flas-tech/cj2-voice-emergency-checklist/ip/trademark_findings.md

# Trademark Availability Screening
## Voice-Driven Emergency Checklist Reader for Aircraft
**Search platform:** USPTO Trademark Search (tmsearch.uspto.gov) · **Date:** June 2026 · **Search type:** wordmark
**Most relevant classes:** IC 009 (electronic/avionics devices, downloadable software), IC 042 (SaaS/software services)

> Not legal advice. A registered trademark attorney should run a full clearance search (state, common-law, and design-mark) before adoption.

## Results by candidate

| # | Name | Live results | Class 9 / 42 conflict | Risk | Verdict |
|---|---|---|---|---|---|
| 1 | AeroVox | 1 | LIVE Class 9 — capacitors (CD Aero LLC, Ser. 77409823) | Moderate | Consult attorney |
| 2 | VoxPilot | 1 | **LIVE Class 9 — speech-recognition software (Reg. 4551726)** | **High** | **Avoid** |
| 3 | AviVox | 0 | None | Clear | Strong candidate |
| 4 | VoxCheck | 0 | None | Clear | Strong candidate |
| 5 | AeroCheck | 1 | LIVE Class 7 — hydraulic check valves (Eaton, Ser. 78433687) | Moderate | Consult attorney |
| 6 | Litany | 2 | None in 9/42 (jewelry, photo website) | Clear but weak | Viable, low distinctiveness |
| 7 | Wingman | 125 live (20+ in Class 9) | Crowded; aviation marks (Beeper Avionics) DEAD | Moderate-High | Caution |
| 8 | CheckCall | 0 | None | Clear | Strong candidate |

## Detail on the decisive ones

- **VoxPilot — AVOID.** Identical wordmark, LIVE/REGISTERED in Class 9 for "software for reporting real-time analytics generated from interactive speech recognition applications" (Reg. No. 4551726, Ser. 86113375). Directly analogous to our voice-recognition product → near-certain refusal and opposition risk.
- **AeroVox — moderate.** LIVE Class 9 registration for capacitors (CD Aero LLC, Ser. 77409823). Different goods, but Class 9 is broad and an examiner could cite it.
- **Wingman — crowded.** 20+ live Class 9 marks (sunglasses, flotation vests, speakers, automotive driver-assist, etc.). Notably, the only *aviation-specific* Wingman marks — Beeper Avionics' "portable electronic device for detecting/locating aircraft" (Ser. 88947677) and "software for generating audible aircraft warnings/checklists" (Ser. 88984394) — are both DEAD/ABANDONED. The aviation niche is technically open but the name is weak and heavily contested.
- **AviVox / VoxCheck / CheckCall — clear.** Zero results in any class. Safest to register; strong inherent distinctiveness (coined/suggestive).
- **Litany — clear but weak.** No 9/42 conflicts, but it's a common English word (low distinctiveness, hard to enforce).

## Recommendation (for the report)
Lead candidate: **AviVox** (coined, aviation + voice, clean across all classes). Backups: **VoxCheck**, **CheckCall**. All three are inherently distinctive and currently unregistered. Confirm common-law/domain use before adoption.
