flas-tech/cj2-voice-emergency-checklist/ip/figures/patent_figures.pdf

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

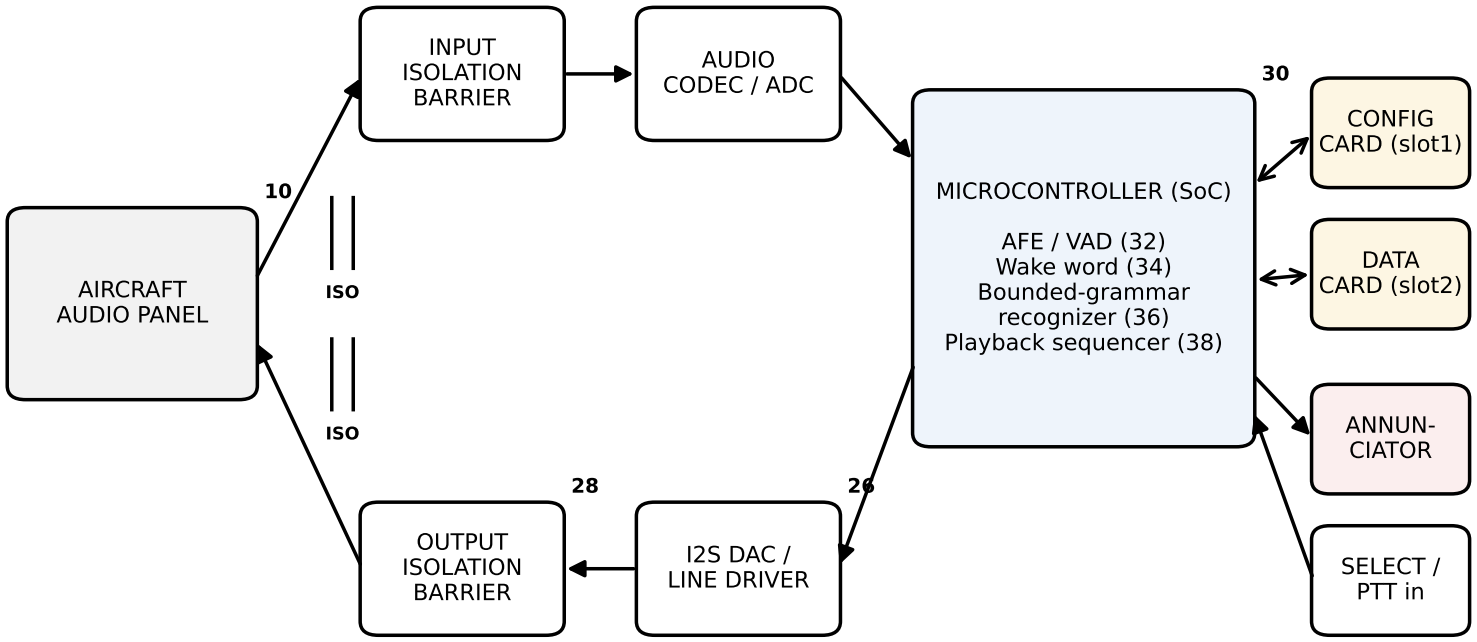
[picture p16: figure]

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

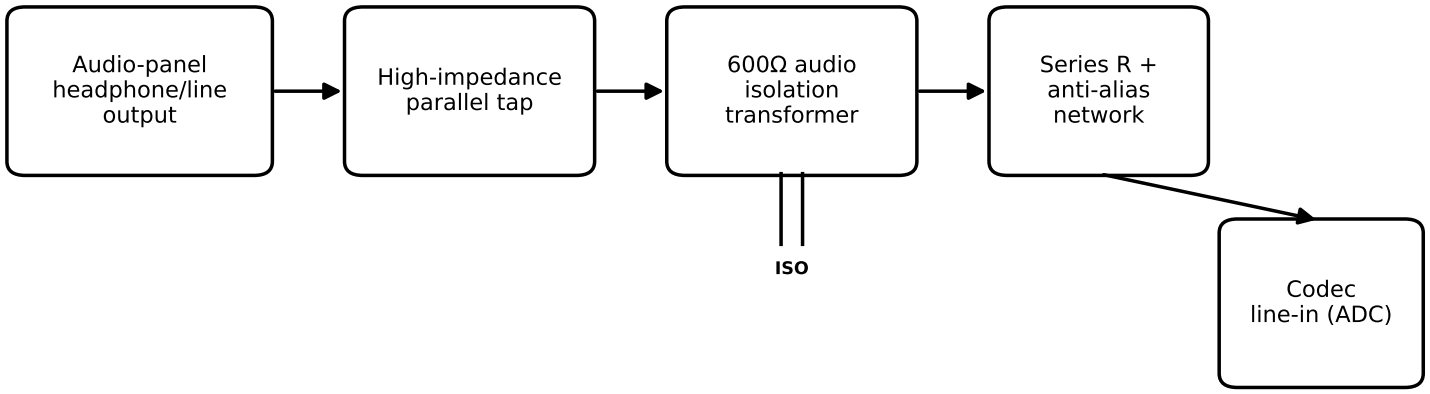
[picture p17: figure]

# FIG. 3

## Digital Audio-Input Embodiment (Buffered, Receive-Only)

10

21b
24

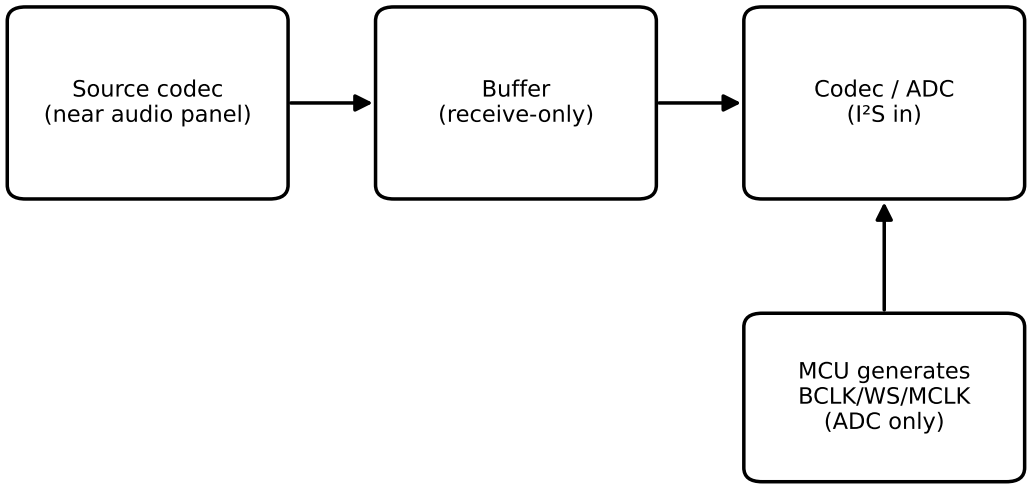
[picture p18: figure]
Source codec (near audio panel); Buffer (receive-only); Codec / ADC (I²S in); MCU generates BCLK/WS/MCLK (ADC only)

25

data: panel device only

All clocks generated locally for the ADC; no data line is driven back toward any aircraft bus.

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

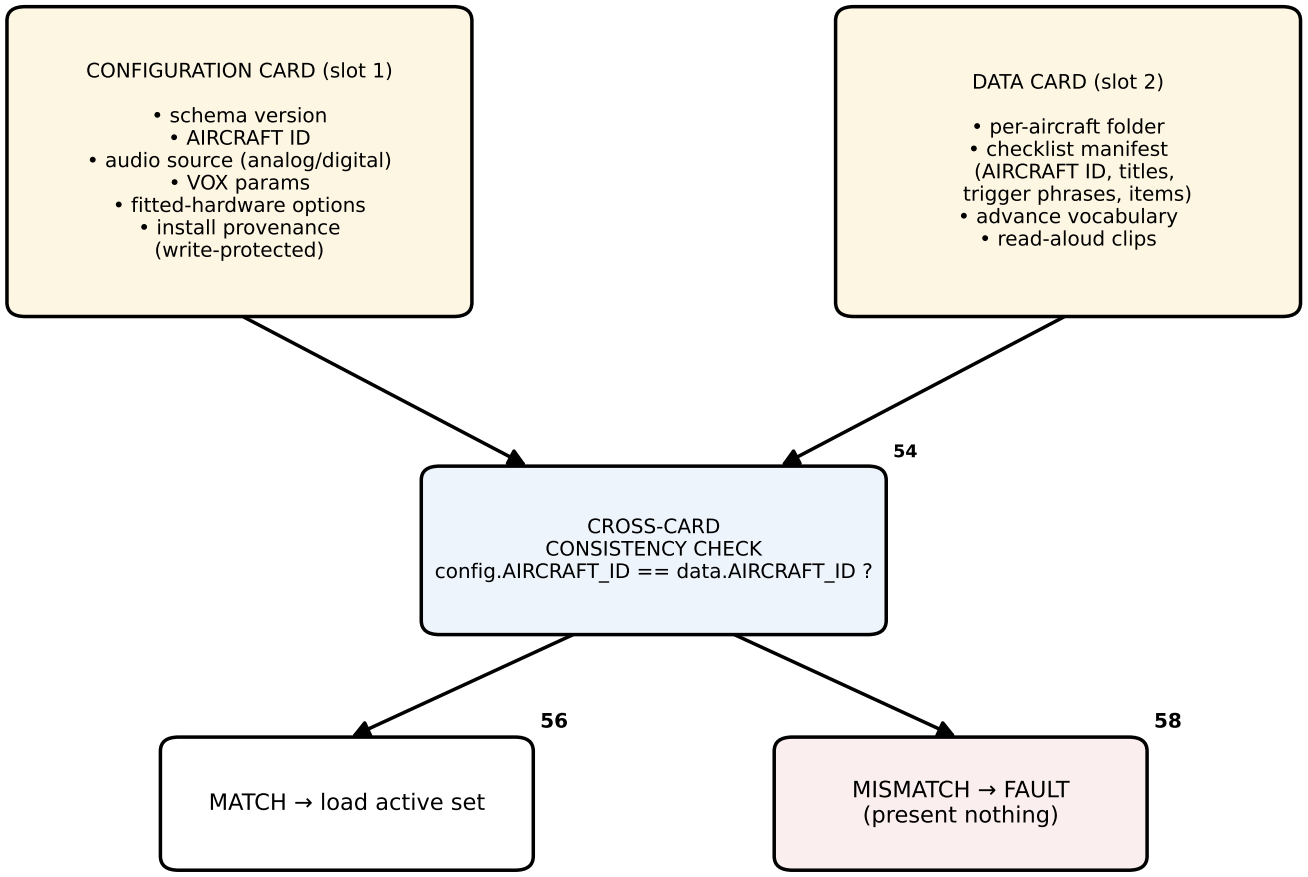
[picture p19: figure]

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

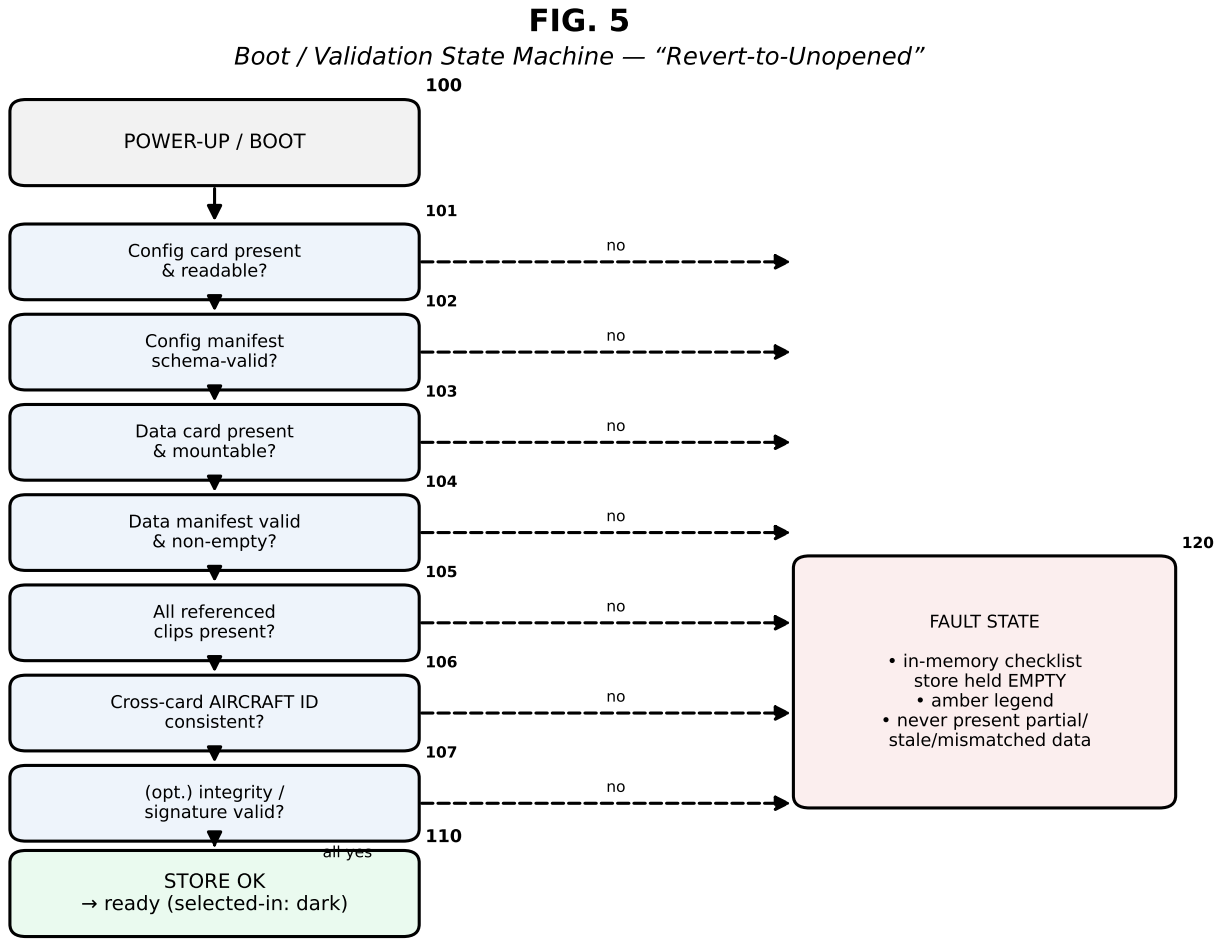
[picture p20: page 5]

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

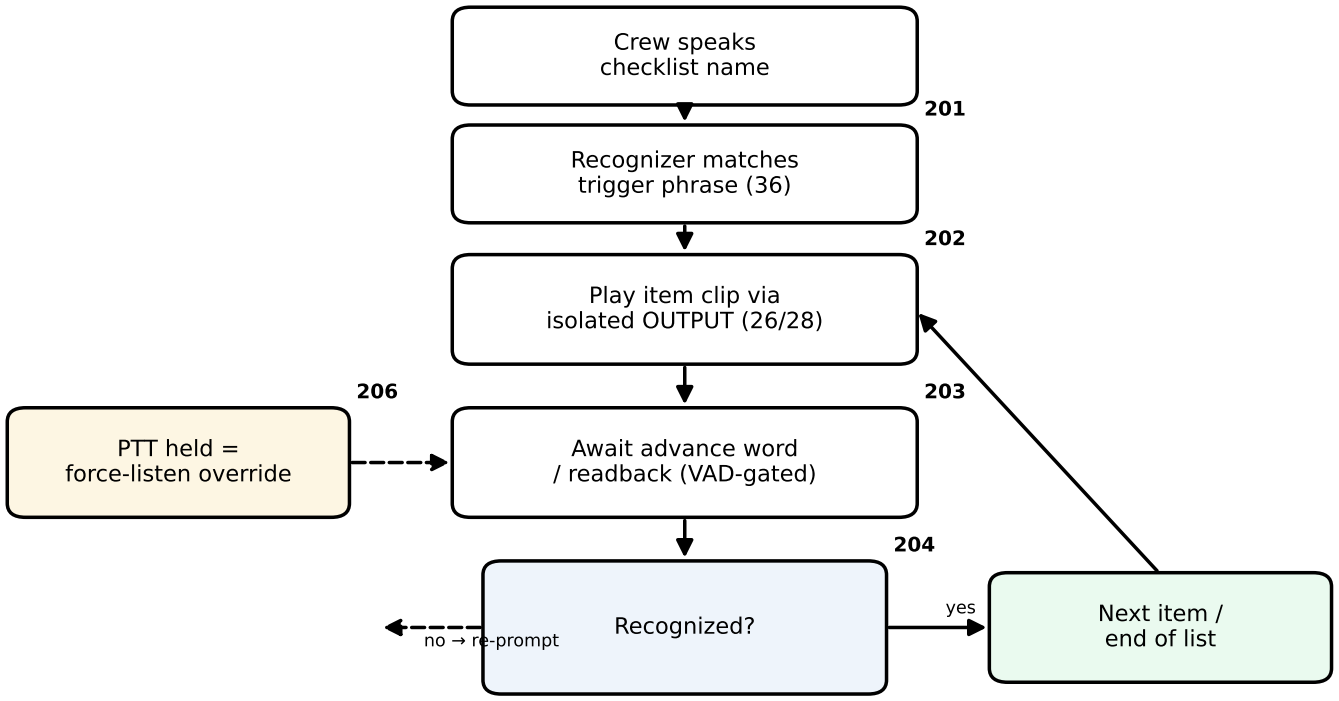
[picture p21: figure]

# FIG. 8

## Card Integrity / Authentication Embodiment

72

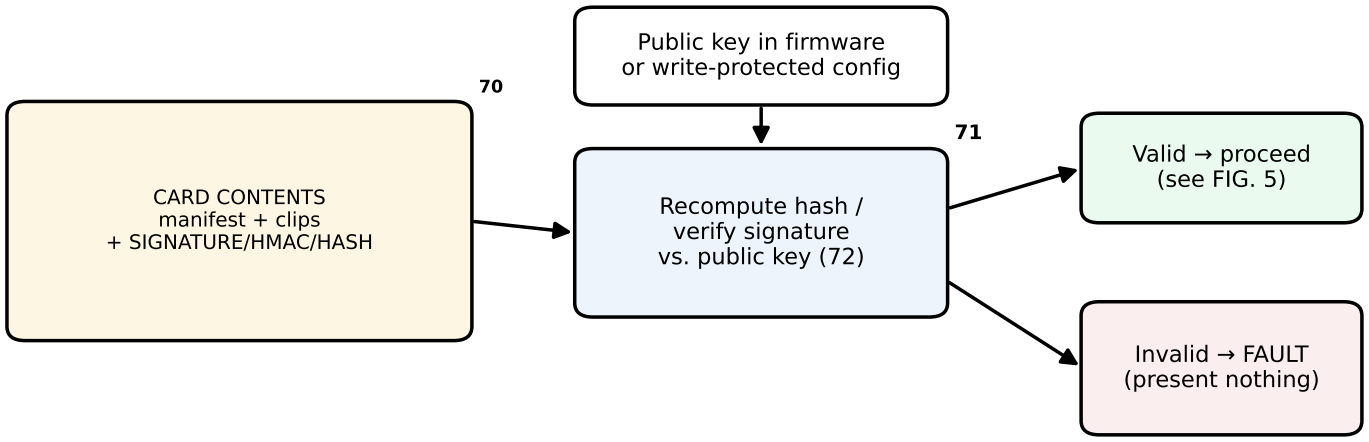
[picture p22: figure]
CARD CONTENTS manifest + clips + SIGNATURE/HMAC/HASH; Recompute hash / verify signature vs. public key (72); Public key in firmware or write-protected config; Valid; proceed; (see FIG. 5); Invalid; FAULT; (present nothing)

73

74

Tampered, corrupted, or unauthenticated cards are rejected under the revert-to-unopened rule.

# FIG. 9

## Tamper-Evident Configuration / Audit Log (Hash-Chained)

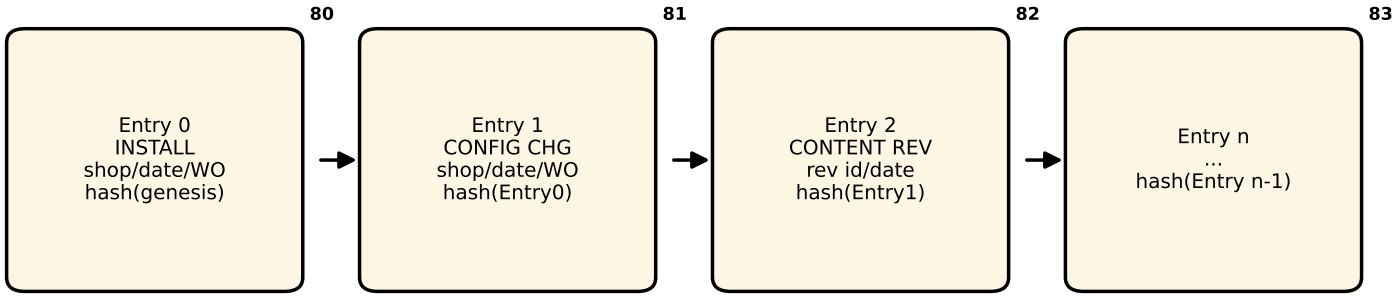
[picture p23: figure]
Entry 0 INSTALL shop/date/WO hash(genesis); Entry 1 CONFIG CHG shop/date/WO hash(Entry0); Entry 2 CONTENT REV rev id/date hash(Entry1); Entry n ... hash(Entry n-1)

Each entry includes a hash over the prior entry; deletion, reordering, or back-dating is detectable by recomputing the chain.

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

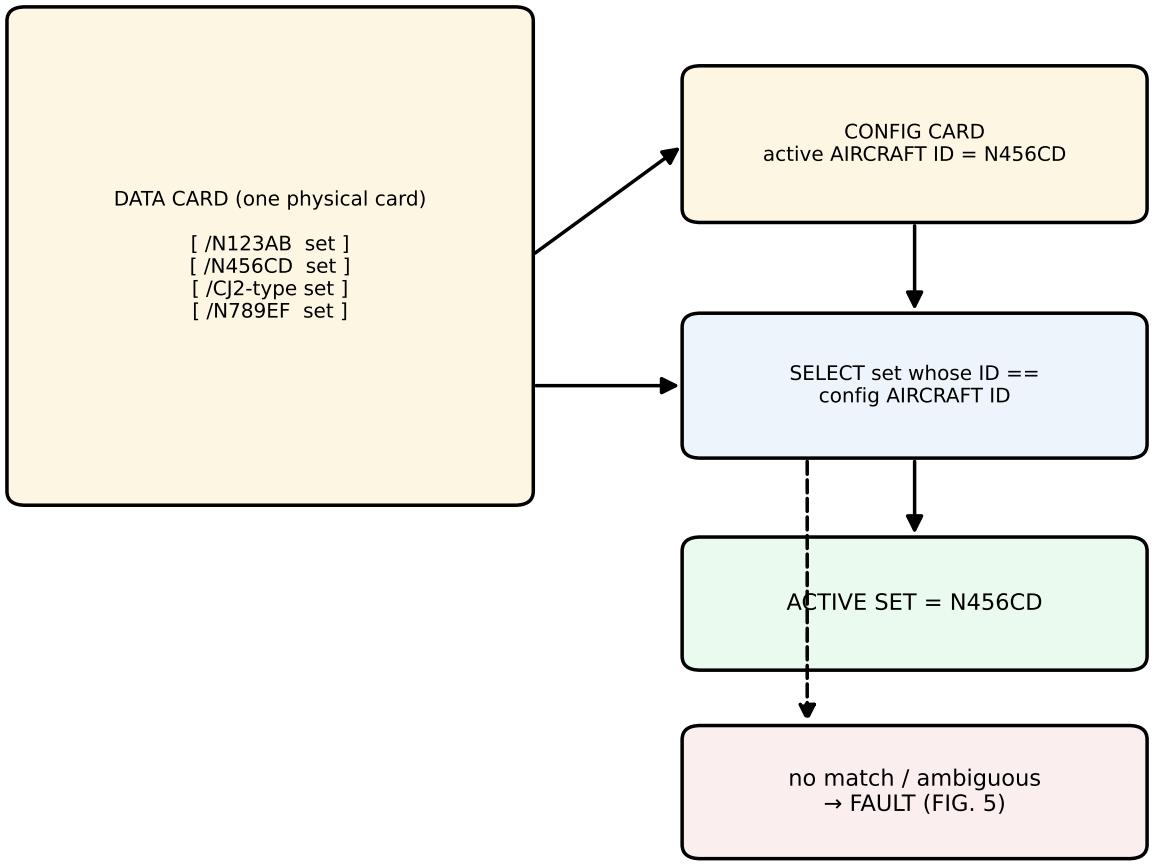
[picture p24: figure]

# FIG. 11

## Active Output-Injection Safeguards (Non-Interference)

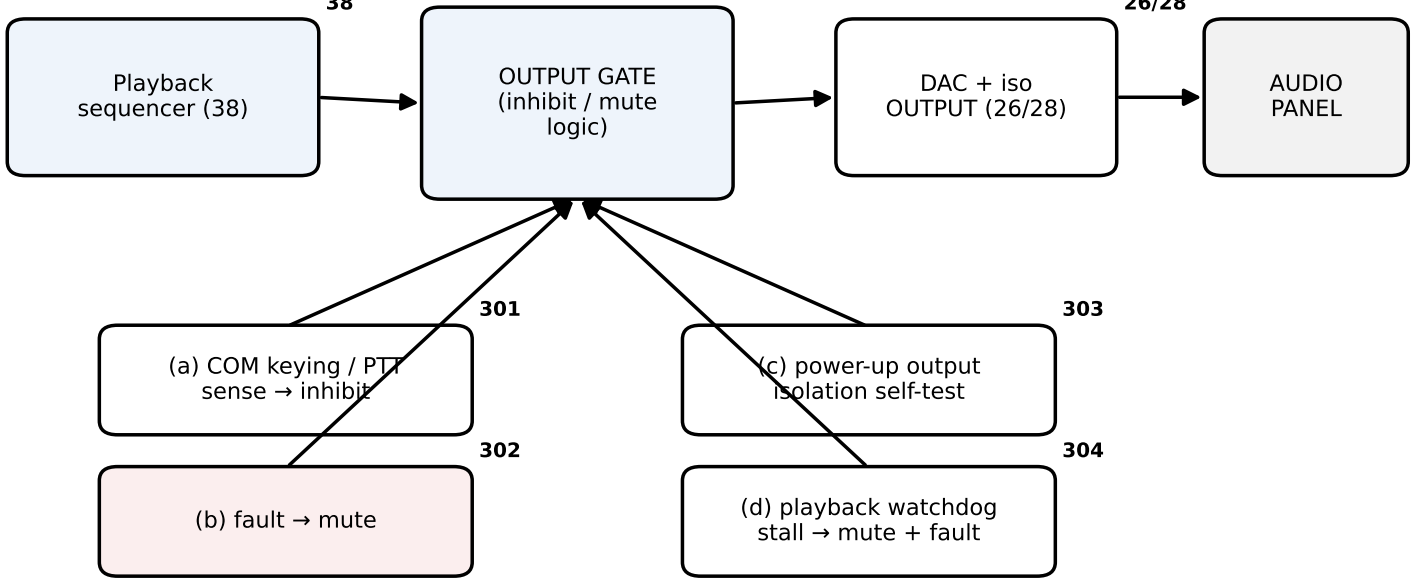
[picture p25: figure]
Playback sequencer (38); OUTPUT GATE (inhibit / mute logic); DAC + iso OUTPUT (26/28); AUDIO PANEL; (a) COM keying / PTT; sense; inhibit; (b) fault; mute; (c) power-up output isolation self-test; (d) playback watchdog; stall; mute + fault

38

300
26/28

10

Non-interference is an actively enforced, testable behavior not merely a passive consequence of the transformer.

# FIG. 12

## No-Mask Audio Arbitration vs. Required Communications

311

312

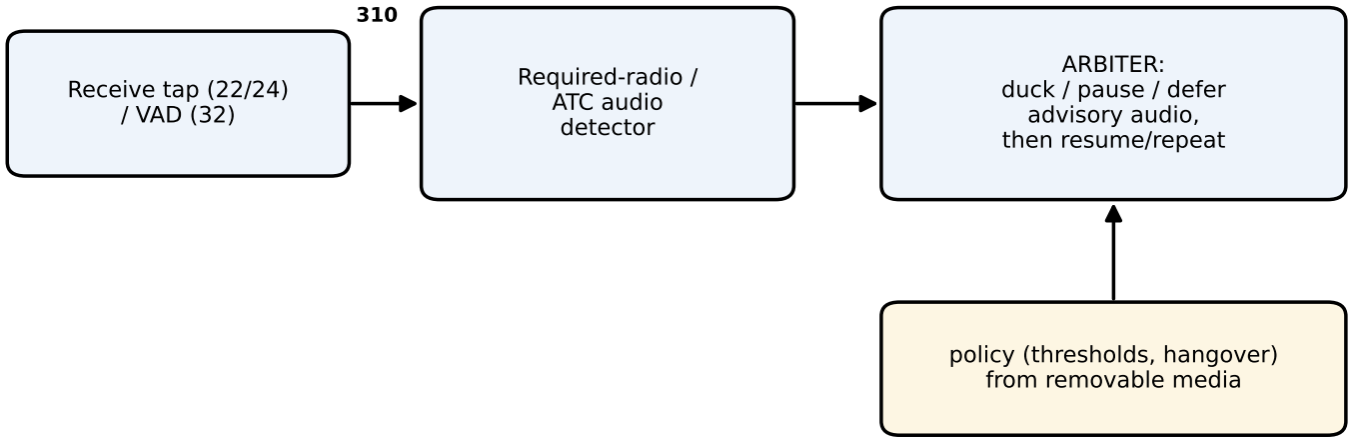
[picture p26: figure]
Receive tap (22/24) / VAD (32); Required-radio / ATC audio detector; ARBITER: duck / pause / defer advisory audio, then resume/repeat; policy (thresholds, hangover) from removable media

313

Advisory read-aloud yields to required communications so a checklist item is delivered intelligibly and never talks over ATC.

# FIG. 13

## Crew Readback Verification (Challenge & Response)

320

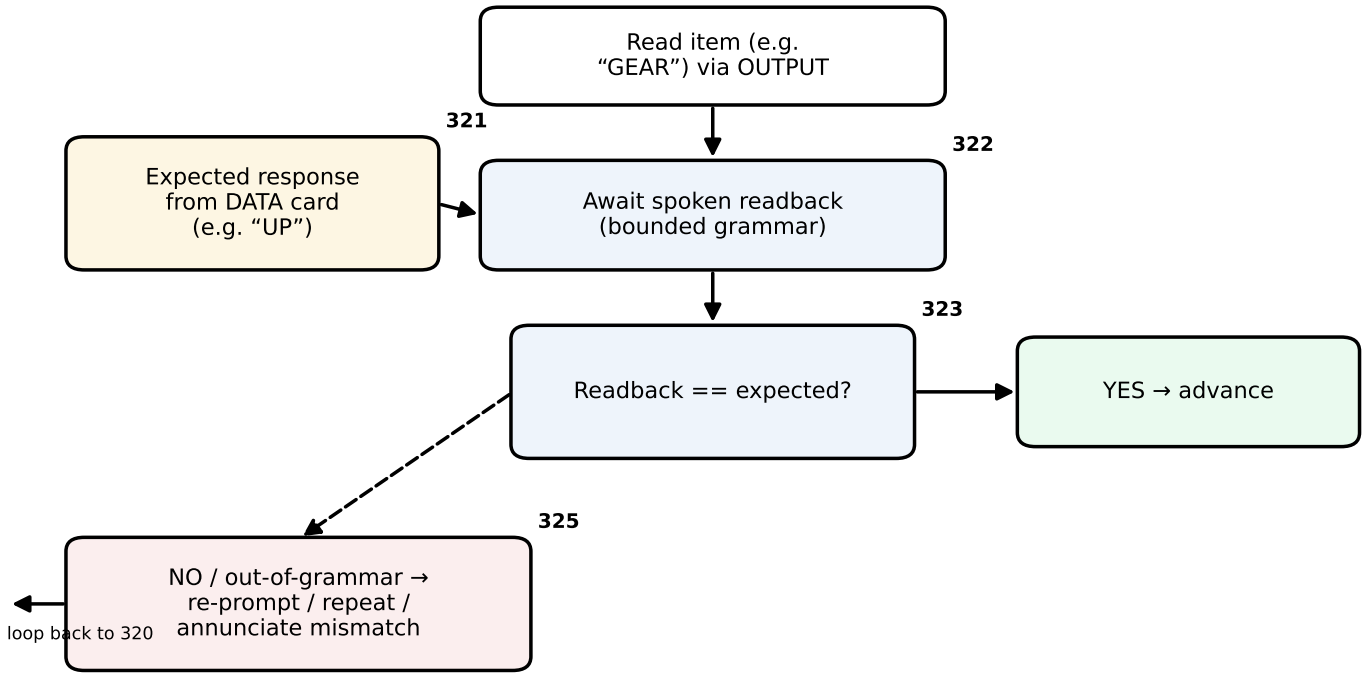
[picture p27: figure]
Read item (e.g. GEAR ) via OUTPUT; Expected response from DATA card (e.g. UP ); Await spoken readback (bounded grammar); Readback == expected?; YES; advance; NO / out-of-grammar re-prompt / repeat / annunciate mismatch; loop back to 320

324

Items may be configured to accept a generic advance word OR a specific verified readback.

# FIG. 14

## Interchangeable Isolation-Barrier Embodiments (Either Channel)

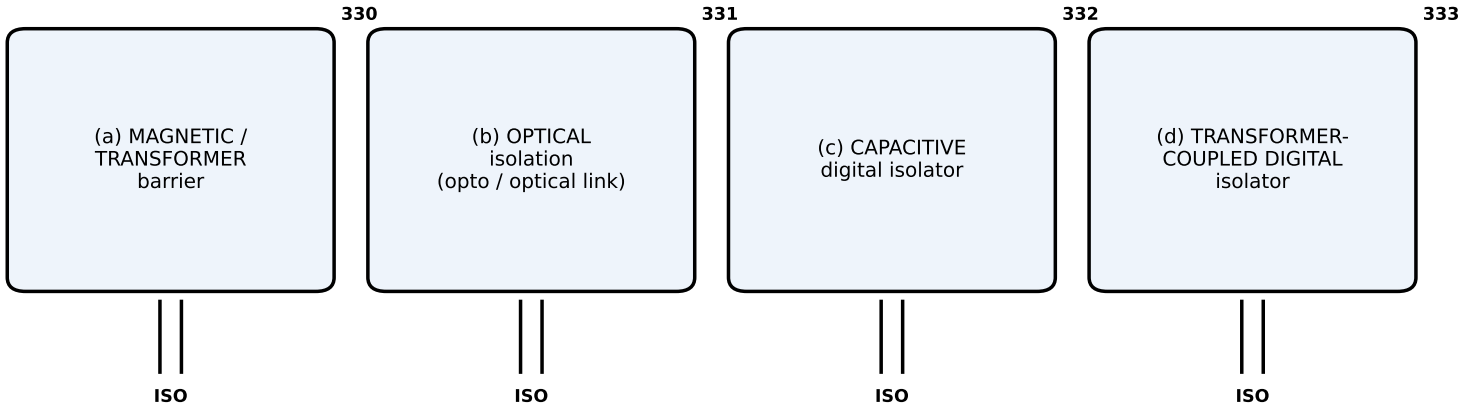
[picture p28: figure]
(a) MAGNETIC / TRANSFORMER barrier; ISO; (b) OPTICAL isolation (opto / optical link); (c) CAPACITIVE digital isolator; (d) TRANSFORMER- COUPLED DIGITAL isolator

Input and output barriers remain INDEPENDENT | no shared conductive path | regardless of which isolation means is used.

Reciting alternatives expressly protects the dual-isolated-channel architecture against substitute-technology design-arounds.
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
