flas-tech/cj2-voice-emergency-checklist/ip/USPTO_SB16_Provisional_Cover_Sheet.md

# USPTO Form PTO/SB/16 — Provisional Application for Patent Cover Sheet

> **NOT LEGAL ADVICE.** This is a pre-filled working draft prepared by an AI assistant, not a patent attorney. Verify every field against the live fillable PDF at
> https://www.uspto.gov/sites/default/files/documents/sb0016.pdf
> and have a registered patent practitioner review before filing. Fields marked **[FILL]** require information only you can supply.

---

## Form identity
- **Form:** PTO/SB/16 (Provisional Application for Patent Cover Sheet)
- **Statutory basis:** 37 CFR 1.51(c)(1)
- **Filing route:** USPTO Patent Center (electronic) — https://patentcenter.uspto.gov

---

## 1. Inventor(s)

This application names **two joint inventors**. Patent Center has an "Add inventor" control — enter both.

### Inventor 1
| Field | Value |
|---|---|
| Given name (first + middle) | Michael **[FILL — confirm full legal middle name/initial]** |
| Family name (last) | Gravalec |
| Residence — City | **[FILL — city of residence]** |
| Residence — State | **[FILL — e.g., FL]** |
| Residence — Country | **[FILL — e.g., US]** |
| Mailing address | **[FILL — street, city, state, ZIP, country]** |

### Inventor 2
| Field | Value |
|---|---|
| Given name (first + middle) | Brandon **[FILL — confirm full legal middle name/initial]** |
| Family name (last) | Cole |
| Residence — City | **[FILL — city of residence]** |
| Residence — State | **[FILL]** |
| Residence — Country | **[FILL]** |
| Mailing address | **[FILL — street, city, state, ZIP, country]** |

> Note: residence for the cover sheet is **where each inventor lives**, not the business address. Use each inventor's actual current residence. Both inventors must be listed; order does not affect rights for joint inventors.

---

## 2. Title of the Invention

Use the **technical** title (brand names like "CheckM8" do not belong in the spec body or title — keep them as a docket reference only, see Section 6):

> **Dual Galvanically-Isolated, Receive-Only Audio-Tap Voice Checklist and Emergency-Procedure Annunciation System with Dual-Card Cross-Consistency Verification and Revert-to-Unopened Recovery**

*(This matches the title on the specification. If you prefer a shorter title, you may use:)*

> **Isolated Voice-Activated Aircraft Checklist and Annunciation System**

**[DECIDE — pick one title; it must match the specification's title exactly.]**

---

## 3. Correspondence Address

| Field | Value |
|---|---|
| Name / firm | **[FILL — your name, or "Flite Line Aviation Services, LLC", or patent attorney's firm]** |
| Address | **[FILL]** |
| City / State / ZIP | **[FILL]** |
| Country | **[FILL]** |
| Telephone | **[FILL]** |
| Email | **[FILL — Patent Center requires a valid email]** |
| Customer Number (if you have one) | **[FILL or leave blank]** |

> In Patent Center you may instead associate a **Customer Number**. If you do not have one, enter the address directly.

---

## 4. Attorney / Agent (if any)

| Field | Value |
|---|---|
| Filing pro se (no attorney)? | **[DECIDE — Yes / No]** |
| Attorney/Agent name | **[FILL if represented]** |
| Registration number | **[FILL if represented]** |
| Docket number | CHECKM8-PROV-001 *(suggested — see Section 6)* |

---

## 5. Entity Status (checkbox on cover sheet / selected in Patent Center)

**[DECIDE — see the entity-status analysis in `USPTO_Inventor_Applicant_Declaration.md`. This is the single most important decision and it is NOT straightforward because the applicant is an LLC.]**

- [ ] Large entity — $320 provisional fee
- [ ] **Small entity** — $160 provisional fee (likely the SAFE choice for an LLC applicant)
- [ ] **Micro entity** — $65 provisional fee (requires LLC gross-income test + Form SB/15A; see caution below)

---

## 6. Docket / Project Reference (internal — not a USPTO field)

- **Project / product reference:** CheckM8
- **Suggested attorney docket number:** `CHECKM8-PROV-001`

> The brand "CheckM8" is fine as a **docket / internal reference**. Per the trademark findings, the recommended commercial mark is **AviVox** (clear), and **VoxPilot should be avoided** (conflicts with Reg. No. 4551726). Do not put brand names in the specification body or title.

---

## 7. U.S. Government Property Interest

- [ ] No U.S. Government agency has a property interest in this application. **[CONFIRM — check this box if true. It is true unless this was developed under a government contract/grant.]**

---

## 8. Number of pages / drawings (Patent Center will ask)

| Item | Count |
|---|---|
| Specification pages | **[FILL after final PDF pagination]** |
| Number of drawing sheets | 14 (FIG. 1–FIG. 14) |
| Drawings included? | Yes — informal drawings (acceptable for provisional per 37 CFR 1.81) |

---

## Signature

The provisional cover sheet itself does **not** require an inventor signature in the same way a declaration does, but Patent Center submission requires a person to certify/sign the electronic submission.

| Field | Value |
|---|---|
| Signature | **[FILL — /Michael Gravalec/ in Patent Center S-signature format]** |
| Name | Michael Gravalec |
| Date | **[FILL — date of filing]** |
| Capacity | Inventor / Applicant representative |

> With two joint inventors, the Patent Center submission may be signed by one inventor, by both, or by a representative of the applicant LLC. Confirm who will sign the electronic submission.
