flas-tech/cj2-voice-emergency-checklist/firmware/docs/wiring_diagram.py

#!/usr/bin/env python3
"""
Generate the CJ2 Voice Emergency Checklist DIY wiring diagram (SVG).
Schematic-style block diagram: ESP32-S3 in the center, peripherals around it,
color-coded nets, and the Applied Avionics split-legend annunciator switch with
its lamp-driver circuit. Pin numbers match firmware/main/board_pins.h.

Run:  python3 wiring_diagram.py   ->  wiring_diagram.svg
"""

W, H = 1600, 1180

# ---- palette ----
BG      = "#0e1320"
PANEL   = "#1a2236"
PANEL2  = "#232d47"
EDGE    = "#3a4663"
INK     = "#e8edf6"
SUB     = "#9fb0cf"
ESP     = "#2a3a5e"
ESPED   = "#4f6aa0"

# net colors
C_3V3   = "#ff5d5d"   # red
C_5V    = "#ff9f43"   # orange
C_GND   = "#5b6577"   # gray
C_I2S_M = "#37d39a"   # green (audio-in I2S)
C_I2S_S = "#36b3ff"   # blue  (audio-out I2S to COM3 isolated output stage)
C_SD    = "#c98bff"   # purple (SD)
C_CTRL  = "#ffd84d"   # yellow (buttons/select)
C_LED   = "#ff7ac0"   # pink  (legend lamps)

parts = []
def esc(s): return s.replace("&","&amp;").replace("<","&lt;").replace(">","&gt;")

def rect(x,y,w,h,fill,stroke=EDGE,rx=10,sw=1.5):
    parts.append(f'<rect x="{x}" y="{y}" width="{w}" height="{h}" rx="{rx}" '
                 f'fill="{fill}" stroke="{stroke}" stroke-width="{sw}"/>')

def text(x,y,s,size=15,fill=INK,anchor="start",weight="400",mono=False,ls="0"):
    fam = "ui-monospace,Menlo,Consolas,monospace" if mono else \
          "Inter,Segoe UI,Helvetica,Arial,sans-serif"
    parts.append(f'<text x="{x}" y="{y}" font-family="{fam}" font-size="{size}" '
                 f'fill="{fill}" text-anchor="{anchor}" font-weight="{weight}" '
                 f'letter-spacing="{ls}">{esc(s)}</text>')

def wire(pts,color,wd=3.0,dash=None):
    d = "M " + " L ".join(f"{x},{y}" for x,y in pts)
    da = f' stroke-dasharray="{dash}"' if dash else ""
    parts.append(f'<path d="{d}" fill="none" stroke="{color}" stroke-width="{wd}" '
                 f'stroke-linecap="round" stroke-linejoin="round"{da}/>')

def dot(x,y,color,r=4.5):
    parts.append(f'<circle cx="{x}" cy="{y}" r="{r}" fill="{color}"/>')

def pin(x,y,label,color,side="left",size=13):
    dot(x,y,color)
    if side=="left":  text(x-10,y+4,label,size,SUB,"end",mono=True)
    else:             text(x+10,y+4,label,size,SUB,"start",mono=True)

# ================= background =================
parts.append(f'<rect width="{W}" height="{H}" fill="{BG}"/>')
# title
text(40,52,"CJ2 Voice Emergency Checklist — DIY Wiring Diagram", 30, INK, weight="700")
text(40,80,"ESP32-S3 + audio-panel input (isolated I2S codec, RX-only) + audio-panel output (isolated TX to COM3 channel) + two microSD (Config + Data) + Applied Avionics split-legend switch",
     16, SUB)
text(40,102,"Pin numbers match firmware/main/board_pins.h   •   DEMO / TRAINING ONLY — NOT FOR FLIGHT", 13, C_5V, weight="600")

# ================= ESP32-S3 (center) =================
ex,ey,ew,eh = 640, 250, 320, 620
rect(ex,ey,ew,eh,ESP,ESPED,rx=16,sw=2.5)
text(ex+ew/2,ey+38,"ESP32-S3", 26, INK,"middle",weight="700")
text(ex+ew/2,ey+62,"DevKitC-1  N16R8", 14, SUB,"middle")
text(ex+ew/2,ey+82,"(PSRAM required for ESP-SR)", 12, C_5V,"middle")

# left-side ESP pins (x = ex)
LX = ex
esp_left = [
    (300,"3V3",  C_3V3),
    (335,"5V",   C_5V),
    (370,"GND",  C_GND),
    (425,"G4  AIN BCLK", C_I2S_M),
    (455,"G5  AIN WS",   C_I2S_M),
    (485,"G6  AIN DIN",  C_I2S_M),
    (515,"G3  AIN MCLK", C_I2S_M),
    (555,"G1  SDA",  C_SD),
    (580,"G2  SCL",  C_SD),
    (615,"G7  CLK",  C_SD),
    (640,"G9  CMD",  C_SD),
    (665,"G8  D0",   C_SD),
    (700,"G47 CFG CD", C_SD),
    (725,"G38 DAT CD", C_SD),
    (765,"G10 SEL",  C_CTRL),
    (790,"G0  PTT",  C_CTRL),
]

# right-side ESP pins (x = ex+ew)
RX = ex+ew
esp_right = [
    (430,"G15 AOUT BCLK", C_I2S_S),
    (465,"G16 AOUT LRC",  C_I2S_S),
    (500,"G17 AOUT DOUT", C_I2S_S),
    (600,"G21 OFF",  C_LED),
    (635,"G14 FLT",  C_LED),
    (700,"G48 STA",  C_CTRL),
]
for y,lab,col in esp_right:
    pin(RX,y,lab,col,"right")

# left pin labels sit just inside, to the LEFT of the pins
for y,lab,col in esp_left:
    dot(LX,y,col)
    text(LX-12,y+4,lab,13,SUB,"end",mono=True)

# ================= AUDIO-PANEL INPUT (top-left) =================
mx,my,mw,mh = 70, 230, 300, 240
rect(mx,my,mw,mh,PANEL,rx=12)
text(mx+16,my+28,"AUDIO-PANEL INPUT", 17, INK,weight="700")
text(mx+16,my+48,"Crew audio from the panel (RX-only)", 11, SUB)
text(mx+16,my+66,"Isolation xfmr + I2S codec ADC", 11, SUB)
text(mx+16,my+84,"analog tap OR buffered digital - selectable", 11, C_5V)
# codec pin stubs (to ESP)
mp = [(my+118,"BCLK",C_I2S_M),(my+138,"WS",C_I2S_M),(my+158,"DOUT",C_I2S_M),
      (my+178,"MCLK",C_I2S_M),(my+200,"SDA",C_SD),(my+220,"SCL",C_SD)]
MPX = mx+mw
for (y,lab,col) in mp:
    dot(MPX,y,col); text(MPX-12,y+4,lab,12,SUB,"end",mono=True)
text(mx+16,my+108,"ES8388/ES7210 (MCLK+I2C) or PCM1808", 10, SUB)
text(mx+16,my+mh-8,"600Ω AGL isolation xfmr + 220-470Ω series", 10, C_5V)

# ================= TWO microSD (left, lower) =================
sx,sy,sw_,sh = 70, 500, 300, 185
rect(sx,sy,sw_,sh,PANEL,rx=12)
text(sx+16,sy+28,"TWO microSD SLOTS", 17, INK,weight="700")
text(sx+16,sy+48,"SDMMC 1-bit (shared)  -  3.3 V  -  FAT32", 11, SUB)
text(sx+16,sy+66,"Slot 1 = CONFIG CARD   Slot 2 = DATA CARD", 11, C_5V)
sdp=[(sy+96,"CLK",C_SD),(sy+116,"CMD",C_SD),(sy+136,"D0/DAT0",C_SD),
     (sy+156,"CFG CD",C_SD),(sy+176,"DAT CD",C_SD)]
SPX=sx+sw_
for (y,lab,col) in sdp:
    dot(SPX,y,col); text(SPX-12,y+4,lab,12,SUB,"end",mono=True)

# ================= AUDIO-PANEL OUTPUT / COM3 (top-right) =================
ax,ay,aw,ah = 1120, 250, 360, 250
rect(ax,ay,aw,ah,PANEL,rx=12)
text(ax+16,ay+28,"AUDIO-PANEL OUTPUT (COM3)", 17, INK,weight="700")
text(ax+16,ay+46,"ISOLATED TX to dedicated aux channel", 11, SUB)
text(ax+16,ay+64,"I2S DAC + isolation xfmr + line-level out", 11, C_5V)
text(ax+16,ay+82,"Cannot key/jam/back-feed required COM channels", 10, C_5V)
text(ax+16,ay+100,"Separate connector from AUDIO IN (RX ONLY)", 10, SUB)
# output stage pins (from ESP)
amp=[(ay+124,"BCLK",C_I2S_S),(ay+148,"LRC",C_I2S_S),(ay+172,"DIN",C_I2S_S)]
for (y,lab,col) in amp:
    dot(ax,y,col); text(ax+12,y+4,lab,12,SUB,"start",mono=True)
text(ax+16,ay+200,"Line-level out -> 600 ohm isolation xfmr", 10, C_5V)
text(ax+16,ay+216,"-> COM3-style audio-panel input", 10, C_5V)
text(ax+16,ay+ah-12,"[bench: MAX98357A substituted on GPIO15/16/17 only]", 10, SUB)
# arrow symbol pointing right toward audio panel
parts.append(f'<path d="M {ax+aw+10},{ay+135} l26,0 m-10,-10 l10,10 l-10,10" '
             f'fill="none" stroke="{C_I2S_S}" stroke-width="2.5" stroke-linecap="round"/>')
text(ax+aw+16, ay+128, "to audio", 11, SUB, "start")
text(ax+aw+16, ay+162, "panel COM3", 11, C_I2S_S, "start")

# ================= ANNUNCIATOR SWITCH (right, lower) =================
gx,gy,gw,gh = 1150, 540, 400, 470
rect(gx,gy,gw,gh,PANEL,rx=14)
text(gx+18,gy+30,"APPLIED AVIONICS", 16, INK,weight="700")
text(gx+18,gy+50,"VIVISUN / Korry split-legend switch", 12, SUB)
text(gx+18,gy+68,"Dark cockpit (FAA AC 25-11)", 11, C_5V)

# legend faceplate
fx,fy,fw,fh = gx+24, gy+86, 170, 120
rect(fx,fy,fw,fh,"#0b0f18","#5a6b8c",rx=8,sw=2)
parts.append(f'<line x1="{fx}" y1="{fy+fh/2}" x2="{fx+fw}" y2="{fy+fh/2}" stroke="#5a6b8c" stroke-width="2"/>')
text(fx+fw/2, fy+34, "VOICE CHKLST", 13, "#dfe6f2","middle",weight="700")
text(fx+fw/2, fy+50, "OFF", 15, "#ffffff","middle",weight="800")
text(fx+fw/2, fy+92, "VOICE CHKLST", 13, "#ffcf6b","middle",weight="700")
text(fx+fw/2, fy+108,"FAULT", 15, "#ffb02e","middle",weight="800")
text(fx-2, fy-6, "TOP = white", 10, "#cfd8ea")
text(fx-2, fy+fh+16, "BOTTOM = amber", 10, "#ffcf6b")

# state table
tx,ty = gx+210, gy+92
text(tx,ty,"STATE  to  LEGEND", 12, INK, weight="700")
rows=[("IN + OK","dark","dark"),("IN + fault","dark","AMBER"),("OUT","WHITE","dark")]
text(tx,ty+22,"Sel.",11,SUB); text(tx+78,ty+22,"OFF",11,SUB); text(tx+140,ty+22,"FAULT",11,SUB)
for i,(s,o,f) in enumerate(rows):
    yy=ty+44+i*22
    text(tx,yy,s,11,INK,mono=True)
    text(tx+78,yy,o,11,("#ffffff" if o!="dark" else SUB))
    text(tx+140,yy,f,11,("#ffb02e" if f!="dark" else SUB))

# lamp-driver sub-circuit
dvx,dvy,dvw,dvh = gx+24, gy+230, gw-48, 210
rect(dvx,dvy,dvw,dvh,PANEL2,rx=10)
text(dvx+14,dvy+24,"LAMP DRIVER (per legend half)", 13, INK,weight="700")
text(dvx+14,dvy+44,"GPIO cannot drive a 28 V lamp directly - use a", 11, SUB)
text(dvx+14,dvy+60,"low-side N-MOSFET / NPN per half.", 11, SUB)
# simple driver schematic
bx = dvx+30; by = dvy+150
# lamp supply rail
text(bx-6, by-82, "+V lamp (5 or 28 V)", 11, C_5V)
wire([(bx,by-72),(bx+220,by-72)], C_5V, 2.5)
# lamp
parts.append(f'<circle cx="{bx+110}" cy="{by-50}" r="16" fill="none" stroke="{C_LED}" stroke-width="2.5"/>')
parts.append(f'<path d="M {bx+99},{by-61} l22,22 M {bx+121},{by-61} l-22,22" stroke="{C_LED}" stroke-width="2"/>')
text(bx+132, by-46, "legend lamp", 10, C_LED)
wire([(bx+110,by-72),(bx+110,by-66)], C_5V, 2.5)        # rail to lamp
wire([(bx+110,by-34),(bx+110,by-10)], C_LED, 2.5)       # lamp to drain
# MOSFET
parts.append(f'<rect x="{bx+96}" y="{by-10}" width="30" height="40" rx="4" fill="{ESP}" stroke="{ESPED}"/>')
text(bx+111, by+14, "Q", 12, INK,"middle",weight="700")
wire([(bx+110,by+30),(bx+110,by+52)], C_GND, 2.5)       # source to GND
text(bx+118, by+50, "GND", 10, SUB)
# gate from GPIO via resistor
wire([(bx-2,by+10),(bx+96,by+10)], C_LED, 2.5)
parts.append(f'<rect x="{bx+34}" y="{by+3}" width="34" height="14" fill="{PANEL}" stroke="{EDGE}"/>')
text(bx+51, by+14, "1k", 9, SUB,"middle")
text(bx-8, by+8, "GPIO21/G14", 10, C_LED, "end")
text(bx+30, by+38, "pulldown 10k to GND (off-state)", 9, SUB)

# ================= SELECT SWITCH + PTT (bottom-left) =================
swx,swy,sww,swh = 70, 730, 300, 160
rect(swx,swy,sww,swh,PANEL,rx=12)
text(swx+16,swy+28,"DISCRETE INPUTS", 16, INK,weight="700")
text(swx+16,swy+52,"SELECT  G10 to GND when IN", 12, C_CTRL,mono=True)
text(swx+16,swy+72,"(active-low, internal pull-up)", 11, SUB)
text(swx+16,swy+98,"PTT OVERRIDE  G0/BOOT to GND", 12, C_CTRL,mono=True)
text(swx+16,swy+118,"(force-listen; VOX is primary)", 11, SUB)
text(swx+16,swy+138,"VOX = AFE VAD on the panel feed", 11, C_5V)
SWPX=swx+sww
dot(SWPX,swy+52,C_CTRL); dot(SWPX,swy+98,C_CTRL)

# ================= power rail box (bottom center) =================
px,py,pw,ph = 470, 920, 700, 200
rect(px,py,pw,ph,PANEL,rx=12)
text(px+18,py+28,"POWER & GROUND", 16, INK,weight="700")
pwr=[("3V3 (red)","ESP32-S3 3V3 -> codec VDD, both microSD VDD", C_3V3),
     ("5V  (orange)","USB/VIN -> output line driver (low-current); lamp rail separate", C_5V),
     ("GND (gray)","common ground - all devices + lamp driver source", C_GND)]
for i,(a,b,c) in enumerate(pwr):
    yy=py+58+i*34
    dot(px+28,yy-4,c,6); text(px+44,yy,a,13,INK,weight="700")
    text(px+210,yy,b,12,SUB)
text(px+18,py+ph-14,"Budget: logic + peripherals < 250 mA; output line driver is low-current (~50 mA max); total USB >= 1 A (speaker amp removed).",
     11, C_5V)

# ===================================================================
#                           WIRES
# ===================================================================
# Audio codec I2S + I2C to ESP left pins (G4/G5/G6/G3 + G1/G2)
wire([(MPX,my+118),(540,my+118),(540,425),(LX,425)], C_I2S_M)  # BCLK G4
wire([(MPX,my+138),(528,my+138),(528,455),(LX,455)], C_I2S_M)  # WS   G5
wire([(MPX,my+158),(516,my+158),(516,485),(LX,485)], C_I2S_M)  # DOUT G6
wire([(MPX,my+178),(504,my+178),(504,515),(LX,515)], C_I2S_M)  # MCLK G3
wire([(MPX,my+200),(492,my+200),(492,555),(LX,555)], C_SD)     # SDA  G1
wire([(MPX,my+220),(480,my+220),(480,580),(LX,580)], C_SD)     # SCL  G2

# two microSD to ESP (shared G7/G9/G8 + card-detects G47/G38)
wire([(SPX,sy+96),(560,sy+96),(560,615),(LX,615)], C_SD)       # CLK G7
wire([(SPX,sy+116),(548,sy+116),(548,640),(LX,640)], C_SD)     # CMD G9
wire([(SPX,sy+136),(536,sy+136),(536,665),(LX,665)], C_SD)     # D0 G8
wire([(SPX,sy+156),(524,sy+156),(524,700),(LX,700)], C_SD)     # CFG CD G47
wire([(SPX,sy+176),(512,sy+176),(512,725),(LX,725)], C_SD)     # DAT CD G38

# Select + PTT override to ESP
wire([(SWPX,swy+52),(575,swy+52),(575,765),(LX,765)], C_CTRL)  # SELECT G10
wire([(SWPX,swy+98),(560,swy+98),(560,790),(LX,790)], C_CTRL)  # PTT override G0

# Audio-out I2S to ESP right pins (G15/G16/G17) -> COM3 isolated output stage
wire([(RX,430),(1140,430),(1140,ay+124),(ax,ay+124)], C_I2S_S) # AOUT BCLK G15
wire([(RX,465),(1128,465),(1128,ay+148),(ax,ay+148)], C_I2S_S) # AOUT LRC  G16
wire([(RX,500),(1116,500),(1116,ay+172),(ax,ay+172)], C_I2S_S) # AOUT DOUT G17

# Legend lamps: GPIO21/G14 -> driver gates (pink), drains to lamps already drawn
# Route from ESP right pins (G21 @600, G14 @635) down to the driver block gate input.
gate_x = gx+24+30-8  # approx bx-8 of first driver instance
wire([(RX,600),(1080,600),(1080,gy+230+160),(gx+24,gy+230+160)], C_LED)  # G21 OFF -> driver
wire([(RX,635),(1095,635),(1095,gy+230+178),(gx+24+18,gy+230+178)], C_LED, 2.6, dash="6 5") # G14 FLT (2nd half)
text(1072, 592, "G21 -> OFF half", 10, C_LED, "end")
text(1072, 628, "G14 -> FAULT half", 10, C_LED, "end")

# Status LED note (G48 onboard)
text(RX+12, 690, "G48 = onboard RGB (status)", 11, SUB)

# ---- legend / key ----
kx,ky = 40, H-150
keys=[("3.3 V",C_3V3),("5 V",C_5V),("GND",C_GND),("Audio-in I2S (RX)",C_I2S_M),
      ("Audio-out I2S (COM3 TX)",C_I2S_S),("SD bus + I2C",C_SD),("Control in",C_CTRL),("Legend lamp",C_LED)]
text(kx,ky-12,"NET KEY",13,INK,weight="700")
for i,(lab,col) in enumerate(keys):
    yy=ky+ (i//4)*26
    xx=kx + (i%4)*150
    parts.append(f'<line x1="{xx}" y1="{yy}" x2="{xx+26}" y2="{yy}" stroke="{col}" stroke-width="4" stroke-linecap="round"/>')
    text(xx+34,yy+4,lab,12,SUB)

svg = f'<svg xmlns="http://www.w3.org/2000/svg" width="{W}" height="{H}" viewBox="0 0 {W} {H}">\n' \
      + "\n".join(parts) + "\n</svg>\n"

import os
out = os.path.join(os.path.dirname(__file__), "wiring_diagram.svg")
with open(out,"w") as f: f.write(svg)
print("wrote", out, len(svg), "bytes")
